QuartzMovement/gamebub/fpga/verilog/handheld/clk_wiz_system_16mhz.v

// file: clk_wiz_system.v
// 
// (c) Copyright 2008 - 2013 Xilinx, Inc. All rights reserved.
// 
// This file contains confidential and proprietary information
// of Xilinx, Inc. and is protected under U.S. and
// international copyright and other intellectual property
// laws.
// 
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
// CRITICAL APPLICATIONS
// Xilinx products are not designed or intended to be fail-
// safe, or for use in any application requiring fail-safe
// performance, such as life-support or safety devices or
// systems, Class III medical devices, nuclear facilities,
// applications related to the deployment of airbags, or any
// other applications that could lead to death, personal
// injury, or severe property or environmental damage
// (individually and collectively, "Critical
// Applications"). Customer assumes the sole risk and
// liability of any use of Xilinx products in Critical
// Applications, subject only to applicable laws and
// regulations governing limitations on product liability.
// 
// THIS COPYRIGHT NOTICE AND DISCLAIMER MUST BE RETAINED AS
// PART OF THIS FILE AT ALL TIMES.
// 
//----------------------------------------------------------------------------
// User entered comments
//----------------------------------------------------------------------------
// None
//
//----------------------------------------------------------------------------
//  Output     Output      Phase    Duty Cycle   Pk-to-Pk     Phase
//   Clock     Freq (MHz)  (degrees)    (%)     Jitter (ps)  Error (ps)
//----------------------------------------------------------------------------
// clk_out_sys___16.77632______0.000______50.0______343.098____147.672
// clk_out_sdram__33.55263______0.000______50.0______259.466____147.672
// clk_out_av__12.25962______0.000______50.0______318.439____147.672
//
//----------------------------------------------------------------------------
// Input Clock   Freq (MHz)    Input Jitter (UI)
//----------------------------------------------------------------------------
// __primary__________50.000____________0.010

`timescale 1ps/1ps

module clk_wiz_system_clk_wiz 

 (// Clock in ports
  // Clock out ports
  output        clk_out_sys,
  output        clk_out_sdram,
  output        clk_out_av,
  // Status and control signals
  input         reset,
  output        locked,
  input         clk_in_50mhz
 );
  // Input buffering
  //------------------------------------
wire clk_in_50mhz_clk_wiz_system;
wire clk_in2_clk_wiz_system;
  assign clk_in_50mhz_clk_wiz_system = clk_in_50mhz;




  // Clocking PRIMITIVE
  //------------------------------------

  // Instantiation of the MMCM PRIMITIVE
  //    * Unused inputs are tied off
  //    * Unused outputs are labeled unused

  wire        clk_out_sys_clk_wiz_system;
  wire        clk_out_sdram_clk_wiz_system;
  wire        clk_out_av_clk_wiz_system;
  wire        clk_out4_clk_wiz_system;
  wire        clk_out5_clk_wiz_system;
  wire        clk_out6_clk_wiz_system;
  wire        clk_out7_clk_wiz_system;

  wire [15:0] do_unused;
  wire        drdy_unused;
  wire        psdone_unused;
  wire        locked_int;
  wire        clkfbout_clk_wiz_system;
  wire        clkfbout_buf_clk_wiz_system;
  wire        clkfboutb_unused;
    wire clkout0b_unused;
   wire clkout1b_unused;
   wire clkout2b_unused;
   wire clkout3_unused;
   wire clkout3b_unused;
   wire clkout4_unused;
  wire        clkout5_unused;
  wire        clkout6_unused;
  wire        clkfbstopped_unused;
  wire        clkinstopped_unused;
  wire        reset_high;

  MMCME2_ADV
  #(.BANDWIDTH            ("OPTIMIZED"),
    .CLKOUT4_CASCADE      ("FALSE"),
    .COMPENSATION         ("ZHOLD"),
    .STARTUP_WAIT         ("FALSE"),
    .DIVCLK_DIVIDE        (1),
    .CLKFBOUT_MULT_F      (12.750),
    .CLKFBOUT_PHASE       (0.000),
    .CLKFBOUT_USE_FINE_PS ("FALSE"),
    .CLKOUT0_DIVIDE_F     (38.000),
    .CLKOUT0_PHASE        (0.000),
    .CLKOUT0_DUTY_CYCLE   (0.5),
    .CLKOUT0_USE_FINE_PS  ("FALSE"),
    .CLKOUT1_DIVIDE       (19),
    .CLKOUT1_PHASE        (0.000),
    .CLKOUT1_DUTY_CYCLE   (0.5),
    .CLKOUT1_USE_FINE_PS  ("FALSE"),
    .CLKOUT2_DIVIDE       (52),
    .CLKOUT2_PHASE        (0.000),
    .CLKOUT2_DUTY_CYCLE   (0.5),
    .CLKOUT2_USE_FINE_PS  ("FALSE"),
    .CLKIN1_PERIOD        (20.000))
  mmcm_adv_inst
    // Output clocks
   (
    .CLKFBOUT            (clkfbout_clk_wiz_system),
    .CLKFBOUTB           (clkfboutb_unused),
    .CLKOUT0             (clk_out_sys_clk_wiz_system),
    .CLKOUT0B            (clkout0b_unused),
    .CLKOUT1             (clk_out_sdram_clk_wiz_system),
    .CLKOUT1B            (clkout1b_unused),
    .CLKOUT2             (clk_out_av_clk_wiz_system),
    .CLKOUT2B            (clkout2b_unused),
    .CLKOUT3             (clkout3_unused),
    .CLKOUT3B            (clkout3b_unused),
    .CLKOUT4             (clkout4_unused),
    .CLKOUT5             (clkout5_unused),
    .CLKOUT6             (clkout6_unused),
     // Input clock control
    .CLKFBIN             (clkfbout_buf_clk_wiz_system),
    .CLKIN1              (clk_in_50mhz_clk_wiz_system),
    .CLKIN2              (1'b0),
     // Tied to always select the primary input clock
    .CLKINSEL            (1'b1),
    // Ports for dynamic reconfiguration
    .DADDR               (7'h0),
    .DCLK                (1'b0),
    .DEN                 (1'b0),
    .DI                  (16'h0),
    .DO                  (do_unused),
    .DRDY                (drdy_unused),
    .DWE                 (1'b0),
    // Ports for dynamic phase shift
    .PSCLK               (1'b0),
    .PSEN                (1'b0),
    .PSINCDEC            (1'b0),
    .PSDONE              (psdone_unused),
    // Other control and status signals
    .LOCKED              (locked_int),
    .CLKINSTOPPED        (clkinstopped_unused),
    .CLKFBSTOPPED        (clkfbstopped_unused),
    .PWRDWN              (1'b0),
    .RST                 (reset_high));
  assign reset_high = reset; 

  assign locked = locked_int;
// Clock Monitor clock assigning
//--------------------------------------
 // Output buffering
  //-----------------------------------

  BUFG clkf_buf
   (.O (clkfbout_buf_clk_wiz_system),
    .I (clkfbout_clk_wiz_system));






  BUFG clkout1_buf
   (.O   (clk_out_sys),
    .I   (clk_out_sys_clk_wiz_system));


  BUFG clkout2_buf
   (.O   (clk_out_sdram),
    .I   (clk_out_sdram_clk_wiz_system));

  BUFG clkout3_buf
   (.O   (clk_out_av),
    .I   (clk_out_av_clk_wiz_system));



endmodule
